frankyhub/Internetradio/kicad/kicad/Wemos UNO.kicad_sch

## KiCad design kicad/kicad/Wemos UNO.kicad_sch (2024-07-07)

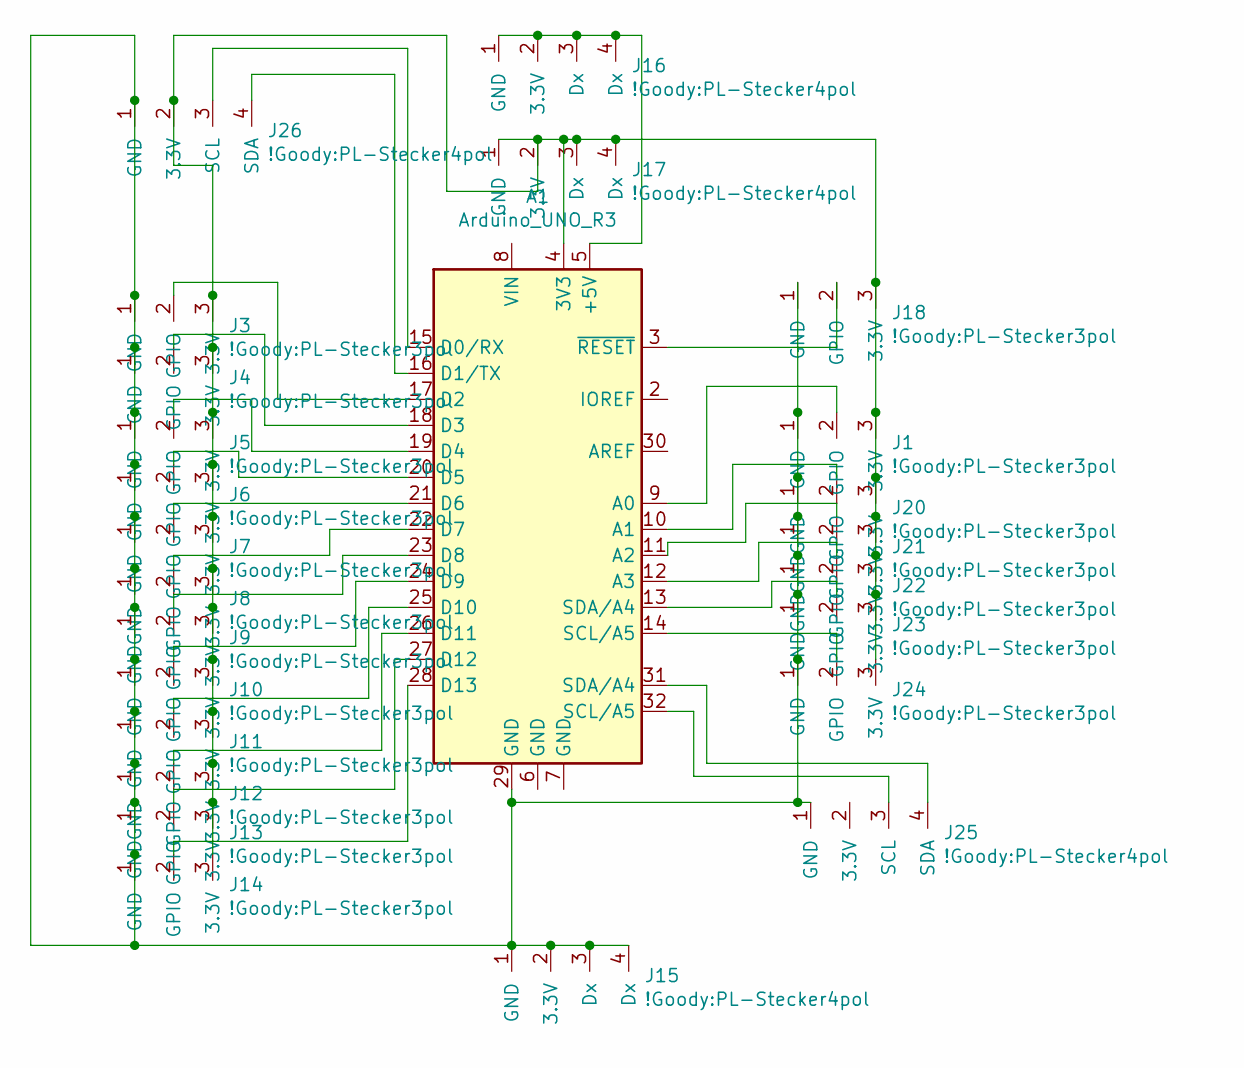
[picture p20: schematic Wemos UNO.kicad_sch]

Parts:
A1: Arduino_UNO_R3
J1, J3, J4, J5, J6, J7, J8, J9, J10, J11, J12, J13, J14, J18, J20, J21, J22, J23, J24: PL-Stecker_3pol; PL-Stecker3pol
J15, J16, J17: PL-Stecker_4pol_Data; PL-Stecker4pol
J25, J26: PL-Stecker_4pol_I2C; PL-Stecker4pol

Connections:
unnamed: A1.3 (~RESET), J18.2 (GPIO)
unnamed: A1.4 (3V3), J1.3 (3.3V), J3.3 (3.3V), J4.3 (3.3V), J5.3 (3.3V), J6.3 (3.3V), J7.3 (3.3V), J8.3 (3.3V), J9.3 (3.3V), J10.3 (3.3V), J11.3 (3.3V), J12.3 (3.3V), J13.3 (3.3V), J14.3 (3.3V), J17.1 (GND), J17.2 (3.3V), J17.3 (Dx), J17.4 (Dx), J18.3 (3.3V), J20.3 (3.3V), J21.3 (3.3V), J22.3 (3.3V), J23.3 (3.3V), J24.3 (3.3V), J26.2 (3.3V)
unnamed: A1.5 (+5V), J16.1 (GND), J16.2 (3.3V), J16.3 (Dx), J16.4 (Dx)
unnamed: A1.9 (A0), J1.2 (GPIO)
unnamed: A1.10 (A1), J20.2 (GPIO)
unnamed: A1.11 (A2), J21.2 (GPIO)
unnamed: A1.12 (A3), J22.2 (GPIO)
unnamed: A1.13 (SDA/A4), J23.2 (GPIO)
unnamed: A1.14 (SCL/A5), J24.2 (GPIO)
unnamed: A1.15 (D0/RX), J26.3 (SCL)
unnamed: A1.16 (D1/TX), J26.4 (SDA)
unnamed: A1.17 (D2), J3.2 (GPIO)
unnamed: A1.18 (D3), J4.2 (GPIO)
unnamed: A1.19 (D4), J5.2 (GPIO)
unnamed: A1.20 (D5), J6.2 (GPIO)
unnamed: A1.21 (D6), J7.2 (GPIO)
unnamed: A1.22 (D7), J8.2 (GPIO)
unnamed: A1.23 (D8), J9.2 (GPIO)
unnamed: A1.24 (D9), J10.2 (GPIO)
unnamed: A1.25 (D10), J11.2 (GPIO)
unnamed: A1.26 (D11), J12.2 (GPIO)
unnamed: A1.27 (D12), J13.2 (GPIO)
unnamed: A1.28 (D13), J14.2 (GPIO)
unnamed: A1.29 (GND), J1.1 (GND), J3.1 (GND), J4.1 (GND), J5.1 (GND), J6.1 (GND), J7.1 (GND), J8.1 (GND), J9.1 (GND), J10.1 (GND), J11.1 (GND), J12.1 (GND), J13.1 (GND), J14.1 (GND), J15.1 (GND), J15.2 (3.3V), J15.3 (Dx), J15.4 (Dx), J18.1 (GND), J20.1 (GND), J21.1 (GND), J22.1 (GND), J23.1 (GND), J24.1 (GND), J25.1 (GND), J26.1 (GND)
unnamed: A1.31 (SDA/A4), J25.4 (SDA)
unnamed: A1.32 (SCL/A5), J25.3 (SCL)
