frankyhub/Internetradio/code/Internetradio_LCD/stations.ino

//https://www.antenne.de/programm/empfang/webradio

//default stationlist
#define DEFAULTSTATIONS 33

//Definition of a set of tested default stations
Station defstations[DEFAULTSTATIONS] PROGMEM = {
  { "https://s10.streamingcloud.online:13552/radioluz320.mp3", "*Radio LuZ", 1 },
  { "http://dispatcher.rndfnk.com/br/br1/nbopf/mp3/low","Bayern1",1},
  { "http://stream.antenne.de/oldie-antenne","Oldie Radio",1},
  { "http://stream.antenne.de/70er-hits","70er-hits",1},
  { "http://stream.antenne.de/80er-kulthits","80er-kulthits",1},
  { "http://stream.antenne.de/classic-rock-live","classic-rock-live",1},
  { "http://1a-rock.radionetz.de:8000/1a-rock.mp3","*1A Rock",1},
  { "http://1a-ndw.radionetz.de/1a-ndw.mp3","*NDW",1},
  { "http://stream.antenne.de/antenne", "Antenne Bayern", 1 },
  { "http://1a-rock.radionetz.de:8000/1a-rock.mp3", "*1A Rock", 1 }, 
  { "http://1a-ndw.radionetz.de/1a-ndw.mp3", "*NDW", 1 }, 
  { "http://dispatcher.rndfnk.com/hr/hr3/suedhessen/high", "HR3", 1 },
  { "http://dispatcher.rndfnk.com/rbb/rbb888/live/mp3/mid", "RBB", 1 },
  { "http://rnrw.cast.addradio.de/rnrw-0182/deinrock/low/stream.mp3", "NRW Rockradio", 1 },  
  { "http://dispatcher.rndfnk.com/rbb/antennebrandenburg/live/mp3/mid", "Antenne Brandenburg", 1 },
  { "http://wdr-wdr2-aachenundregion.icecastssl.wdr.de/wdr/wdr2/aachenundregion/mp3/128/stream.mp3", "WDR 2", 1 },
  { "http://wdr-wdr3-live.icecastssl.wdr.de/wdr/wdr3/live/mp3/128/stream.mp3", "WDR3", 1 },
  { "http://streams.radiobob.de/bob-national/mp3-192/mediaplayer", "BOB", 1 },
  { "http://mdr-284280-1.cast.mdr.de/mdr/284280/1/mp3/low/stream.mp3", "MDR", 1 },
  { "http://icecast.ndr.de/ndr/njoy/live/mp3/128/stream.mp3", "N-JOY", 1 },
  { "http://stream01.zogl.net:8906/stream", "Radino", 1 },
  { "http://radio.toggo.de/live/mp3-192/radio.toggo.de/", "Toggo", 1 },
  { "http://stream.laut.fm/hoerspiel", "Hörspiele", 1 },
  { "http://stream.laut.fm/jugend_radio", "Jugend", 1 },
  { "http://646.cloudrad.io:8234", "Strobe", 1 },
  { "http://646.cloudrad.io:8276", "Pulse107", 1 },
  { "http://646.cloudrad.io:8314", "DJ Perry", 1 },
  { "http://rnrw.cast.addradio.de/rnrw-0182/dein90er/low/stream.mp3", "NRW 90er", 1 },
  { "http://stream.1a-webradio.de/saw-deutsch/", "1A Deutsche Hits", 1 },
  { "http://dispatcher.rndfnk.com/br/brklassik/live/mp3/low", "Bayern Klassik", 1 },
  { "http://rnrw.cast.addradio.de/rnrw-0182/deinschlager/low/stream.mp3", "NRW Schlagerradio", 1 },
  { "http://rt1.radio/tu6h1", "RT1 Rock", 1 },
  { "http://stream.streambase.ch/vrock/mp3-192/", "Virgin Radio", 1 }
};



void setup_senderList() {
  char nkey[4];
  char ukey[4];
  char fkey[4];
  for (uint8_t i = 0; i<STATIONS; i++) {
    sprintf(nkey,"n%i",i);
    sprintf(ukey,"u%i",i);
    sprintf(fkey,"f%i",i);
    if (i<DEFAULTSTATIONS) {
      strlcpy(stationlist[i].name,sender.getString(nkey,defstations[i].name).c_str(),32);
      strlcpy(stationlist[i].url,sender.getString(ukey,defstations[i].url).c_str(),150);
      stationlist[i].enabled = sender.getUChar(fkey,defstations[i].enabled);
    } else {
      strlcpy(stationlist[i].name,sender.getString(nkey,nkey).c_str(),32);
      strlcpy(stationlist[i].url,sender.getString(ukey,"").c_str(),150);
      stationlist[i].enabled = sender.getUChar(fkey,0);
    }
  }
}

void restore() {
  char nkey[4];
  char ukey[4];
  char fkey[4];
  for (uint8_t i = 0; i<STATIONS; i++) {
    sender.clear();
    sprintf(nkey,"n%i",i);
    sprintf(ukey,"u%i",i);
    sprintf(fkey,"f%i",i);
    if (i<DEFAULTSTATIONS) {
      strlcpy(stationlist[i].name,defstations[i].name,32);
      sender.putString(nkey,defstations[i].name);
      strlcpy(stationlist[i].url,defstations[i].url,150);
      sender.putString(ukey,defstations[i].url);
      stationlist[i].enabled = defstations[i].enabled;
      sender.putUChar(fkey,defstations[i].enabled);
    } else {
      strlcpy(stationlist[i].name,nkey,32);
      sender.putString(nkey,nkey);
      strlcpy(stationlist[i].url,"",150);
      sender.putString(ukey,"");
      stationlist[i].enabled = 0;
      sender.putUChar(fkey,0);
    }
  }
}

void saveList() {
  char nkey[4];
  char ukey[4];
  char fkey[4];
  for (uint8_t i = 0; i<STATIONS; i++) {
    sprintf(nkey,"n%i",i);
    sprintf(ukey,"u%i",i);
    sprintf(fkey,"f%i",i);
    sender.putString(nkey,stationlist[i].name);
    sender.putString(ukey,stationlist[i].url);
    sender.putUChar(fkey,stationlist[i].enabled);
  }
}

void reorder(uint8_t oldpos, uint8_t newpos) {
  Station temp;
  if ((oldpos < STATIONS) && (newpos  < STATIONS)) {
    if (oldpos > newpos) {
      memcpy(&temp,&stationlist[oldpos],sizeof(Station));
      for (uint8_t i = oldpos; i>newpos; i--) {
        memcpy(&stationlist[i],&stationlist[i-1],sizeof(Station));
      }
      memcpy(&stationlist[newpos],&temp,sizeof(Station));
    } else {
      memcpy(&temp,&stationlist[oldpos],sizeof(Station));
      for (uint8_t i = oldpos; i<newpos; i++) {
        memcpy(&stationlist[i],&stationlist[i+1],sizeof(Station));
      }
      memcpy(&stationlist[newpos],&temp,sizeof(Station));
    }
  }
}
